laofahai/vibe-lamp/firmware/test/test_render_engine/test_main.cpp

#include <unity.h>
#include "render_engine.h"

static Rgb px;  // 单像素缓冲

static Session mk(State s, ToolKind t = ToolKind::NONE) {
  return Session{ s, t, /*state_since_ms*/0, /*pulse_at_ms*/0 };
}

void test_empty_sessions_is_idle_dark() {
  render(nullptr, 0, /*now*/0, &px, 1);
  TEST_ASSERT_EQUAL_UINT8(0, px.r);
  TEST_ASSERT_EQUAL_UINT8(0, px.g);
  TEST_ASSERT_EQUAL_UINT8(0, px.b);
}

void test_needs_you_is_reddish() {
  Session s = mk(State::NEEDS_YOU);
  render(&s, 1, /*now*/0, &px, 1);   // t=0：闪烁相位为「亮」
  TEST_ASSERT_GREATER_THAN_UINT8(100, px.r);
  TEST_ASSERT_LESS_THAN_UINT8(60, px.g);
  TEST_ASSERT_LESS_THAN_UINT8(60, px.b);
}

void test_working_code_is_bluish() {
  Session s = mk(State::WORKING, ToolKind::CODE);
  render(&s, 1, /*now*/0, &px, 1);   // t=0：呼吸相位最亮
  TEST_ASSERT_GREATER_THAN_UINT8(px.r, px.b);  // 蓝 > 红
}

// 工具函数：按相位取亮度，断言「呼吸」在波峰/波谷不同
void test_working_breathes() {
  Session s = mk(State::WORKING, ToolKind::CODE);
  s.state_since_ms = 0;
  Rgb peak, trough;
  render(&s, 1, 1000, &peak,   1);   // 半周期 → 三角波波峰（最亮，周期 2000ms）
  render(&s, 1, 0,    &trough, 1);   // 相位 0 → 三角波波谷（最暗）
  TEST_ASSERT_GREATER_THAN_UINT8(peak.b / 2, peak.b);     // 占位避免优化
  TEST_ASSERT_TRUE(trough.b < peak.b);                    // 暗于波峰
}

void test_needs_you_blinks_off() {
  Session s = mk(State::NEEDS_YOU);
  s.state_since_ms = 0;
  Rgb on, off;
  render(&s, 1, 0,   &on,  1);   // 慢闪：亮半周期
  render(&s, 1, 600, &off, 1);   // 暗半周期（周期 1200ms）
  TEST_ASSERT_GREATER_THAN_UINT8(100, on.r);
  TEST_ASSERT_LESS_THAN_UINT8(30, off.r);   // 灭
}

void test_done_fades_out() {
  Session s = mk(State::DONE);
  s.state_since_ms = 0;
  Rgb early, late;
  render(&s, 1, 0,    &early, 1);   // 刚完成：亮
  render(&s, 1, 4000, &late,  1);   // 4s 后：基本暗（渐暗窗 ~4500ms）
  TEST_ASSERT_GREATER_THAN_UINT8(100, early.g);
  TEST_ASSERT_LESS_THAN_UINT8(early.g, late.g + 1);  // late 不亮于 early
  TEST_ASSERT_LESS_THAN_UINT8(40, late.g);
}

void test_error_is_steady_red() {
  Session s = mk(State::ERROR);
  s.state_since_ms = 0;
  Rgb early, later;
  render(&s, 1, 0,   &early, 1);
  render(&s, 1, 500, &later, 1);
  TEST_ASSERT_GREATER_THAN_UINT8(120, early.r);
  TEST_ASSERT_EQUAL_UINT8(early.r, later.r);
}

void test_two_sessions_split_ring() {
  Rgb leds[16];
  Session ss[2] = {
    mk(State::WORKING, ToolKind::CODE),   // 蓝
    mk(State::NEEDS_YOU)                   // 红
  };
  ss[0].state_since_ms = 0; ss[1].state_since_ms = 0;
  render(ss, 2, 0, leds, 16);
  // 前 8 颗偏蓝，后 8 颗偏红
  TEST_ASSERT_GREATER_THAN_UINT8(leds[0].r, leds[0].b);
  TEST_ASSERT_GREATER_THAN_UINT8(leds[15].b, leds[15].r);
}

void test_single_session_fills_all() {
  Rgb leds[16];
  Session s = mk(State::WORKING, ToolKind::CODE);
  s.state_since_ms = 0;
  render(&s, 1, 0, leds, 16);
  for (int i = 0; i < 16; ++i)
    TEST_ASSERT_GREATER_THAN_UINT8(leds[i].r, leds[i].b);  // 全蓝
}

void test_boot_scans() {
  Rgb leds[16];
  Session s = mk(State::BOOT);
  s.state_since_ms = 0;
  render(&s, 1, 0,   leds, 16);   // t=0 亮点在头部
  Rgb head0 = leds[0];
  render(&s, 1, 200, leds, 16);   // 稍后亮点移动
  TEST_ASSERT_TRUE(head0.b != leds[0].b || head0.g != leds[0].g);
}

// —— 计划 05：渲染设置运行时化 ——
void test_default_settings_match_legacy() {
  render_set_settings(render_default_settings());
  Session s = mk(State::WORKING, ToolKind::CODE);
  render(&s, 1, 0, &px, 1);          // 默认蓝呼吸波峰，蓝 > 红（与计划01一致）
  TEST_ASSERT_GREATER_THAN_UINT8(px.r, px.b);
}

void test_custom_color_applied() {
  RenderSettings cfg = render_default_settings();
  cfg.col_done = Rgb{10, 20, 200};   // 把"完成"改成蓝
  render_set_settings(cfg);
  Session s = mk(State::DONE);
  s.state_since_ms = 0;
  render(&s, 1, 0, &px, 1);
  TEST_ASSERT_GREATER_THAN_UINT8(px.r, px.b);   // 现在完成是蓝
}

void test_brightness_scales_output() {
  RenderSettings cfg = render_default_settings();
  cfg.brightness = 64;               // 1/4 亮度
  render_set_settings(cfg);
  Session s = mk(State::NEEDS_YOU);
  s.state_since_ms = 0;
  render(&s, 1, 0, &px, 1);          // needs_you 闪烁亮相位，但被亮度压到 ~1/4
  TEST_ASSERT_LESS_THAN_UINT8(120, px.r);
}

void test_animations_off_is_static() {
  RenderSettings cfg = render_default_settings();
  cfg.animations = false;
  render_set_settings(cfg);
  Session s = mk(State::NEEDS_YOU);
  s.state_since_ms = 0;
  Rgb on, later;
  render(&s, 1, 0,   &on,    1);
  render(&s, 1, 600, &later, 1);     // 关动画：两个相位应一致（不再慢闪到灭）
  TEST_ASSERT_EQUAL_UINT8(on.r, later.r);
}

void setUp() { render_set_settings(render_default_settings()); }
void tearDown() {}

int main() {
  UNITY_BEGIN();
  RUN_TEST(test_empty_sessions_is_idle_dark);
  RUN_TEST(test_needs_you_is_reddish);
  RUN_TEST(test_working_code_is_bluish);
  RUN_TEST(test_working_breathes);
  RUN_TEST(test_needs_you_blinks_off);
  RUN_TEST(test_done_fades_out);
  RUN_TEST(test_error_is_steady_red);
  RUN_TEST(test_two_sessions_split_ring);
  RUN_TEST(test_single_session_fills_all);
  RUN_TEST(test_boot_scans);
  RUN_TEST(test_default_settings_match_legacy);
  RUN_TEST(test_custom_color_applied);
  RUN_TEST(test_brightness_scales_output);
  RUN_TEST(test_animations_off_is_static);
  return UNITY_END();
}
